ZeniteSolar/MAB19/firmware/src/sleep.h

/**
 * @file watchdog.h
 *
 * @defgroup SLEEP Sleep Module
 *
 * @brief A simple sleep module. Note that some interruption should be
 * configured to wake the device even in SLEEP_MODE_IDLE.
 *
 *
 */

#ifndef SLEEP_H
#define SLEEP_H 

#include <avr/io.h>
#include <avr/sleep.h>

void sleep_init(void)
{
	set_sleep_mode(SLEEP_MODE_IDLE);
}

#endif /* ifndef SLEEP_H */
