ZeniteSolar/MAB19/firmware/src/watchdog.h

/**
 * @file watchdog.h
 *
 * @defgroup WATCHDOG Watchdog Module
 *
 * @brief A simple watchdog.
 *
 * A simple way to test the watchdog is to not call wdt_reset() and let it acts.
 *
 */

#ifndef WATCHDOG_H
#define WATCHDOG_H 

#include <avr/io.h>
#include <avr/wdt.h>

/**
 * @brief This function is called upon a HARDWARE RESET:
 */
void wdt_first(void) __attribute__((naked)) __attribute__((section(".init3")));

/**
 * @brief Clear SREG_I on hardware reset.
 */
void wdt_first(void)
{
    MCUSR = 0; // clear reset flags
    wdt_disable();
    //http://www.atmel.com/webdoc/AVRLibcReferenceManual/FAQ_1faq_softreset.html
}

/**	
 * @brief initialize watchdog with some predefined time
 */
void wdt_init(void)
{
    wdt_enable(WDTO_4S);
}

#endif /* ifndef WATCHDOG_H */
